karolorlamowski/self-bal-bot/cad-models/Self-balancing-robot-3dmodel_2021-Jan-07_03-23-42PM-000_CustomizedView23257882860_png_alpha.png

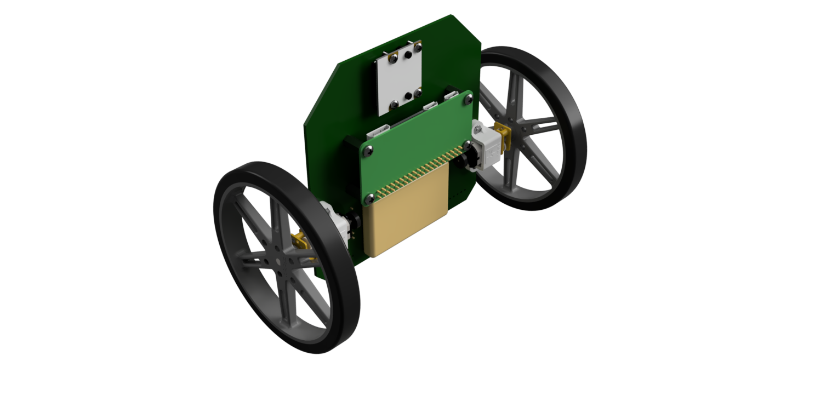
cad-models/Self-balancing-robot-3dmodel_2021-Jan-07_03-23-42PM-000_CustomizedView23257882860_png_alpha.png
