karolorlamowski/self-bal-bot/datasheets/motor-encoder-wiring.png

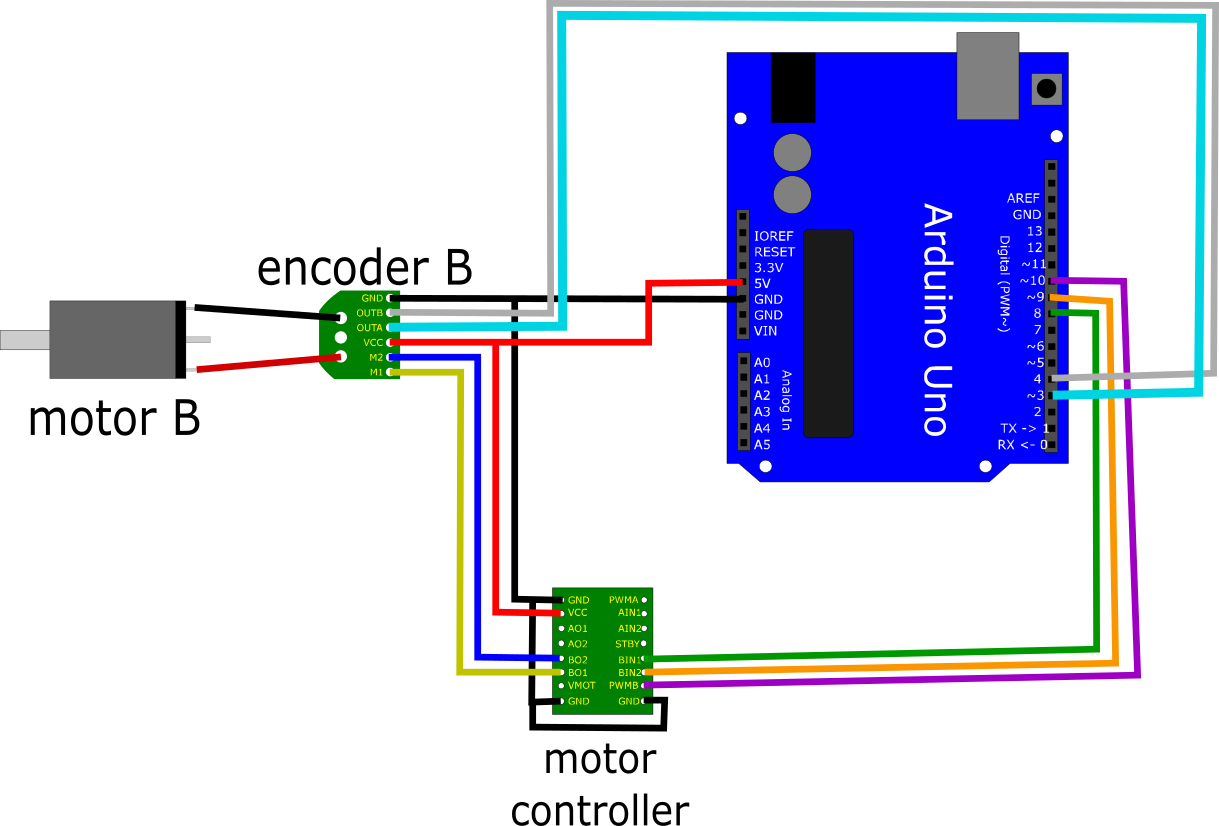
datasheets/motor-encoder-wiring.png
